ben-xo/vu2/framestate.h

/*
 * Copyright Ben XO https://github.com/ben-xo All rights reserved.
 */


#ifndef _FRAMESTATE_H
#define _FRAMESTATE_H

#include <Arduino.h>

struct Framestate
{
  // tempo.cpp
  uint16_t frame_counter = 0;

  // general
  uint8_t vu_width = 0;
  uint8_t mode = 0;
  uint8_t last_mode = 0;
  uint8_t min_vu = 0;
  uint8_t max_vu = 255;

  // buttons.cpp
  uint8_t clicks = 0;
  uint16_t last_push = 0;

  // general
  bool auto_mode:1;
  bool is_new_mode:1;
  bool is_silent:1;
  bool is_attract_mode:1;
  bool is_beat_1:1;
  bool is_beat_2:1;

  // buttons.cpp
  bool pushed:1;
  bool is_down:1;

};

extern struct Framestate F;

void setup_initial_framestate();
#endif /* _FRAMESTATE_H */
