ben-xo/vu2/color_wheels.h

/*
 * Copyright Ben XO https://github.com/ben-xo All rights reserved.
 */
#include "effects.h"

CRGB Wheel(byte WheelPos);
CRGB Wheel2(byte WheelPos);
CRGB Wheel3(byte WheelPos);
CRGB Wheel_Purple_Yellow(byte WheelPos);
