ben-xo/vu2/fps.h

/*
 * Copyright Ben XO https://github.com/ben-xo All rights reserved.
 */

#ifndef _FPS_H
#define _FPS_H

#include <Arduino.h>
#include "config.h"
#include "fps_constants.h"
#include "gpio0.h"

extern uint32_t start_time;   // time each loop started.
extern uint32_t silent_since; // time we've been silent since.

void setup_fps();

/*
 * Busy-wait until the end of the frame, then clear the end-of-frame flag.
 */
inline __attribute__((always_inline)) static void reach_target_fps()
{
  uint32_t end_time = micros();
  while(!(GPIOR0 & (END_OF_FRAME_FLAG))) {
    asm("");
  }
  GPIOR0 &= ~(END_OF_FRAME_FLAG);
  start_time = end_time;
}


#endif /* _FPS_H */
