ben-xo/vu2/fps_constants.h

/*
 * Copyright Ben XO https://github.com/ben-xo All rights reserved.
 */

#ifndef _FPS_CONSTANTS_H
#define _FPS_CONSTANTS_H

#include "config.h"
#include "pwm_constants.h"

#define FPS_INTERRUPT_RESET_VAL (PWM_LED_FRQ / FPS)

#endif /* _FPS_CONSTANTS_H */
