ben-xo/vu2/PeckettIIRFixedPoint.h

/*
 * Copyright Ben XO https://github.com/ben-xo All rights reserved.
 */

#ifndef _PECKETTIIRFIXEDPOINT_H
#define _PECKETTIIRFIXEDPOINT_H

#include "config.h"

void PeckettIIRFixedPointSetup();
bool PeckettIIRFixedPoint(uint8_t val, bool is_beat);

#endif /* _PECKETTIIRFIXEDPOINT_H */
