ben-xo/vu2/plume.h

/*
 * Copyright Ben XO https://github.com/ben-xo All rights reserved.
 */

#include "framestate.h"
#include "effects.h"
//#include "plume_map.h"
#include "color_wheels.h"

void render_stream_pixels();
void render_shoot_pixels(uint8_t peakToPeak, bool is_beat);
